sachi1645/Analog-Computer/LT_Spice_Simulations/Adder.asc

R1: res; 1K; tol=1 pwr=0.1
R2: res; 1K; tol=1 pwr=0.1
R3: res; 1K; tol=1 pwr=0.1
R4: res; 1K; tol=1 pwr=0.1
U1: AD744
V1: voltage; 12
V2: voltage; 12
V3: voltage; SINE(0 4 1000); AC 1
V4: voltage; SINE(0 2 200); AC 1
Named nets: 0, V_addin_1, V_addin_2, V_add_out, +12, -12
.tran 20m
.ac dec 10 1 20K
