sachi1645/Analog-Computer/LT_Spice_Simulations/Differentiator.asc

C1: cap; 100n
C2: cap; 1µ
R1: res; 1K; tol=1 pwr=0.1
R3: res; 1K; tol=1 pwr=0.1
R4: res; 1k; tol=1 pwr=0.1
U1: AD744
V1: voltage; 12
V2: voltage; 12
V3: voltage; PULSE(0 4 0 0 0 10m 100m 10); AC 1
Named nets: V_diff_out, 0, V_diffin_1, +12, -12
.tran 500m
.ac dec 10 1 20K
