sachi1645/Analog-Computer/LT_Spice_Simulations/Gilbertcell_Multiplier.asc

C1: cap; 10µ
C2: cap; 10µ
C3: cap; 10µ
C4: cap; 1µ
C5: cap; 1µ
Q1: npn; 2N3904
Q2: npn; 2N3904
Q3: npn; 2N3904
Q4: npn; 2N3904
Q5: npn; 2N3904
Q6: npn; 2N3904
R1: res; 270
R2: res; 270
R3: res; 270
R4: res; 4.7k
R5: res; 3.3k
R6: res; 2.2k
R7: res; 2.2k
R8: res; 2.2k
R9: res; 2.2k
R10: res; 2.2k
R11: res; 50
R12: res; 50
R13: res; 1k
R14: res; 1k
R15: res; 1k
R16: res; 100k
R17: res; 1k
R18: res; 100k
R19: res; 1k
R20: res; 1k
R22: res; 33k
R23: res; 1k
U4: AD744
U5: AD744
U6: AD744
U7: AD744
V1: voltage; 12
V2: voltage; 12
V3: voltage; 12
V4: voltage; SINE(0 2 2k)
V5: voltage; SINE(0 3 500)
V6: voltage; 15
V7: voltage; 15
Named nets: 0, +V, -V, V1, V2, Vout
.tran 30m
variable reisitor to adjust output gain
