sachi1645/Analog-Computer/LT_Spice_Simulations/Iintegrator.asc

C3: cap; 1µ
R2: res; 1K; tol=1 pwr=0.1
R4: res; 1K; tol=1 pwr=0.1
U1: AD744
V1: voltage; 12
V2: voltage; 12
V3: voltage; PULSE(0 4 0 0 0 2m 5m 10); AC 1
Named nets: V_Diff_in, V_Diff_out, 0, +12, -12
.tran 20m
.ac dec 10 1 20K
