sachi1645/Analog-Computer/LT_Spice_Simulations/LogAntilog_Multiplier_FullWave.asc

D1: diode; 1N4148
D2: diode; 1N4148
D3: diode; 1N4148
D4: diode; 1N4148
D5: diode; 1N4148
D6: diode; 1N4148
R1: res; 1K; tol=1 pwr=0.1
R2: res; 10K; tol=1 pwr=0.1
R3: res; 10K; tol=1 pwr=0.1
R4: res; 1K; tol=1 pwr=0.1
R5: res; 1k; tol=1 pwr=0.1
R6: res; 2.55k; tol=1 pwr=0.1
R7: res; 1k; tol=1 pwr=0.1
R8: res; 1k; tol=1 pwr=0.1
R9: res; 1k; tol=1 pwr=0.1
R10: res; 100k; tol=1 pwr=0.1
R11: res; 1k; tol=1 pwr=0.1
R12: res; 100k; tol=1 pwr=0.1
U1: AD744
U2: AD744
U3: AD744
U4: AD744
U5: AD744
U6: AD744
U7: AD744
V1: voltage; 12
V2: voltage; 12
V3: voltage; SINE(0 3 500)
V4: voltage; SINE(0 2 30)
Named nets: Vs+, Vs-, 0, V_mulin_2, V_mulin_1, V_mulout
.tran 100m
Variable Resistor to Adjust Ouyput Gain
