sachi1645/Analog-Computer/LT_Spice_Simulations/Regulator_12v.asc

C1: cap; 2200µ
C2: cap; 2200µ
D1: diode; 1N4007
D2: diode; 1N4007
D3: diode; 1N4007
D4: diode; 1N4007
L: ind2; 5m
Ls1: ind2; 13µ
Ls2: ind2; 13µ
U1: 7812
U2: 7912
V1: voltage; SINE(0 300 50); Rser=0.001
Named nets: 0, +12v, -12v, GND
K. L Ls1 Ls2 1
.tran 100m
